electricalhog/PD_Charger/KiCad/EPC-KiCad-Library/Ki3DModels/D0375.step

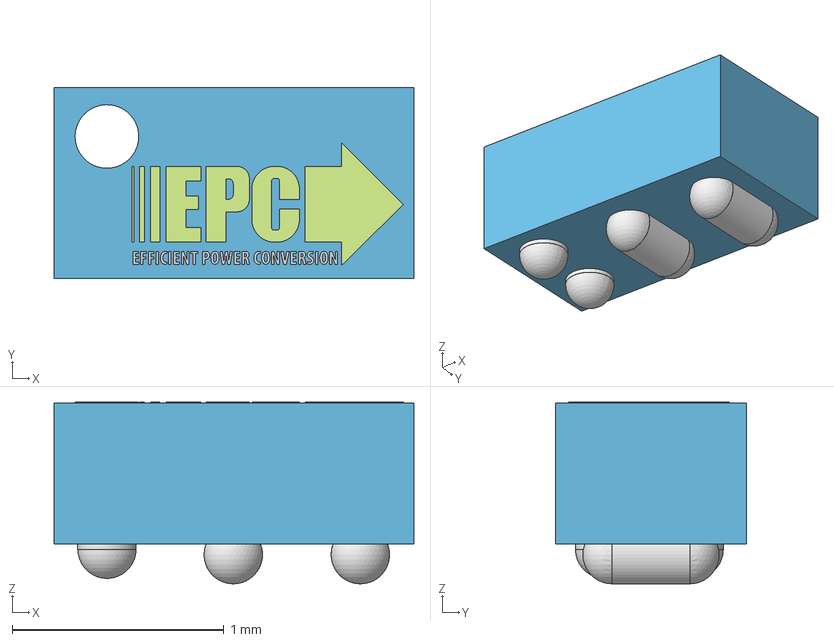
[picture p19: CAD file, 2024-12-06]
KiCad/EPC-KiCad-Library/Ki3DModels/D0375.step
1.70 x 0.9 x 0.858 mm
1.25mm
1.25mm001
1.25mm002
1.25mm003
1.25mm004
1.25mm005
1.25mm006
Extruded
