electricalhog/PD_Charger/KiCad/EPC-KiCad-Library/Ki3DModels/D0551.step

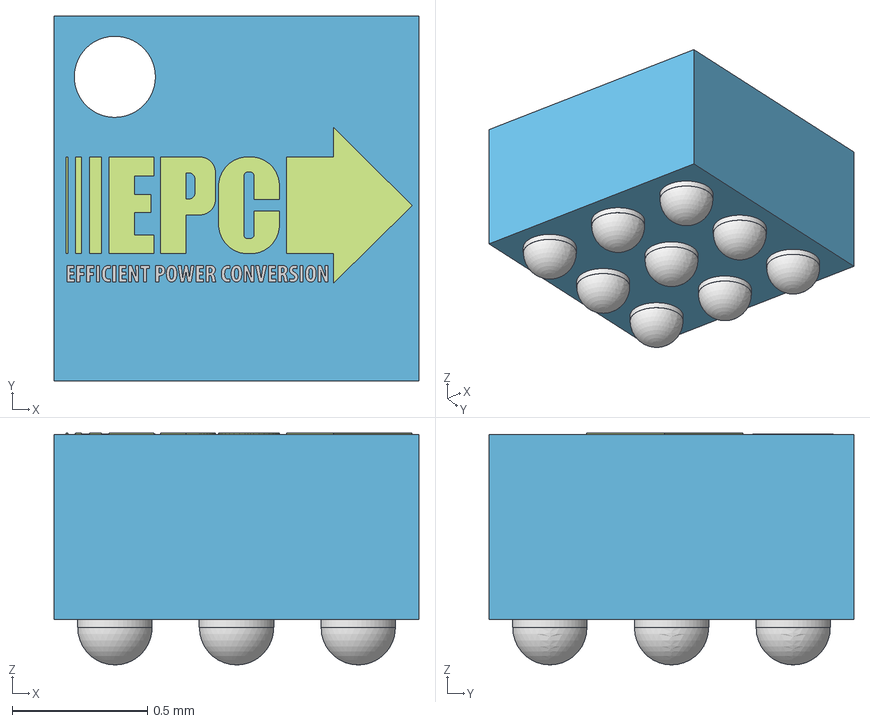
[picture p20: CAD file, 2024-12-06]
KiCad/EPC-KiCad-Library/Ki3DModels/D0551.step
1.35 x 1.35 x 0.857 mm
1.25mm
1.25mm001
1.25mm002
1.25mm003
1.25mm004
1.25mm005
1.25mm006
Extruded
