electricalhog/PD_Charger/KiCad/EPC-KiCad-Library/Ki3DModels/D0683.step

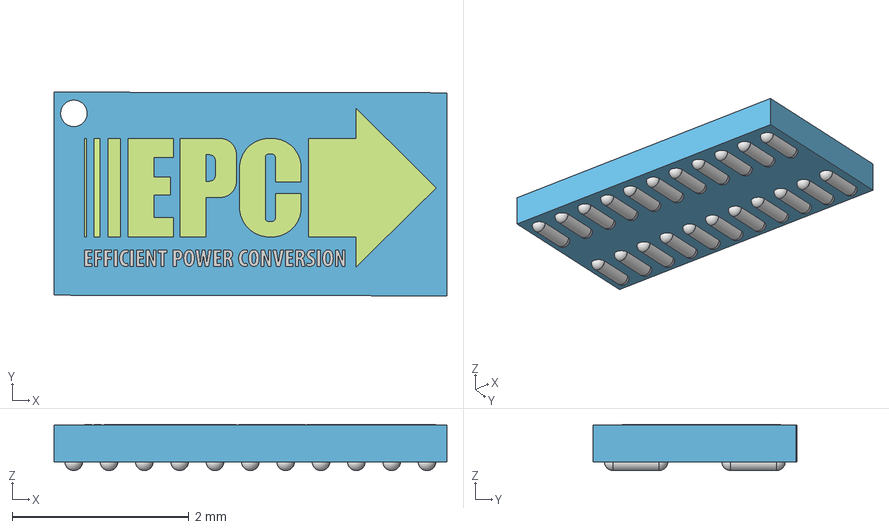
[picture p21: CAD file, 2024-12-06]
KiCad/EPC-KiCad-Library/Ki3DModels/D0683.step
4.45 x 2.31 x 0.523 mm
Green001
Green002
Green003
Green004
Green005
Green006
Green007
Extruded
