electricalhog/PD_Charger/KiCad/EPC-KiCad-Library/Ki3DModels/D0034.step

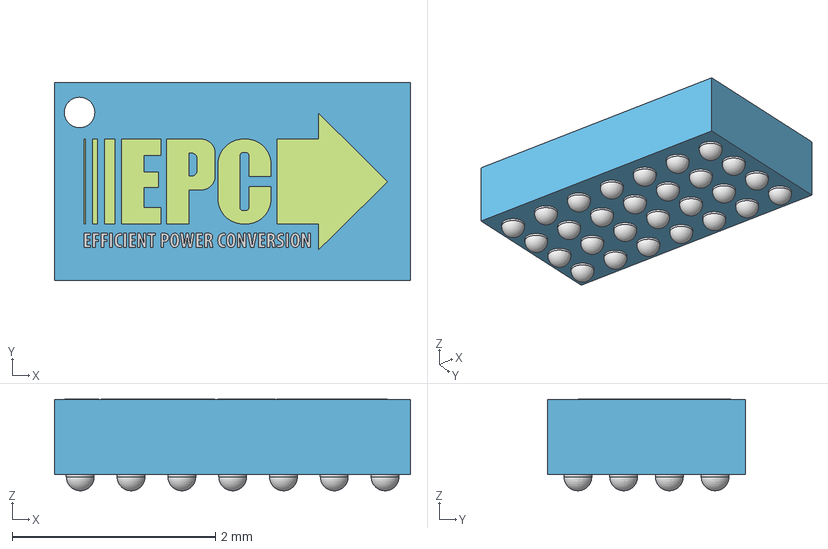
[picture p22: CAD file, 2024-12-06]
KiCad/EPC-KiCad-Library/Ki3DModels/D0034.step
3.50 x 1.95 x 0.902 mm
Green001
Green002
Green003
Green004
Green005
Green006
Green007
Extruded
