electricalhog/PD_Charger/KiCad/EPC-KiCad-Library/Ki3DModels/D0265.step

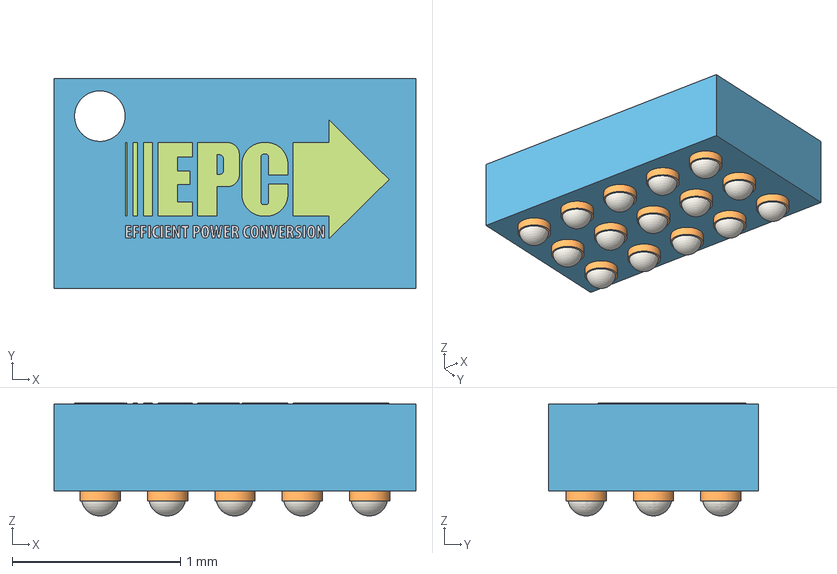
[picture p23: CAD file, 2024-12-06]
KiCad/EPC-KiCad-Library/Ki3DModels/D0265.step
2.15 x 1.25 x 0.671 mm
1.5mm
1.5mm001
1.5mm002
1.5mm003
1.5mm004
1.5mm005
1.5mm006
Extruded
