electricalhog/PD_Charger/KiCad/EPC-KiCad-Library/Ki3DModels/D0122.step

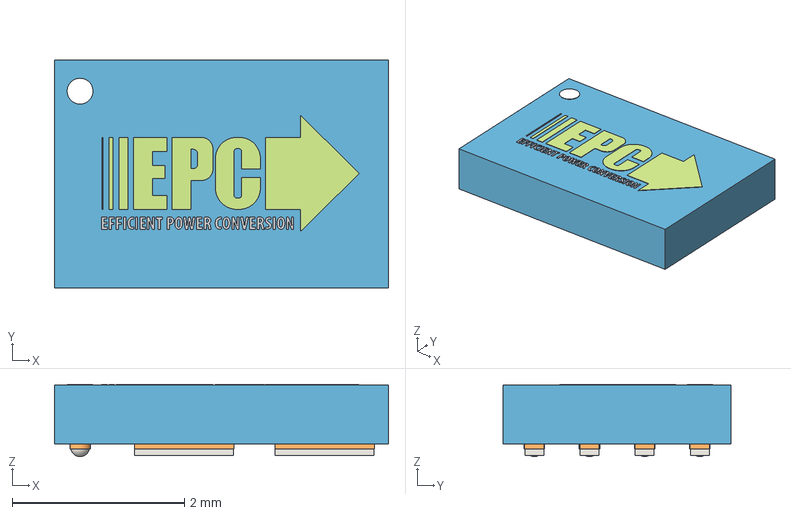
[picture p24: CAD file, 2024-12-06]
KiCad/EPC-KiCad-Library/Ki3DModels/D0122.step
3.88 x 2.64 x 0.838 mm
Green001
Green002
Green003
Green004
Green005
Green006
Green007
Extruded
Extruded001 x 8
Extruded002 x 8
