electricalhog/PD_Charger/KiCad/EPC-KiCad-Library/Ki3DModels/D0298.step

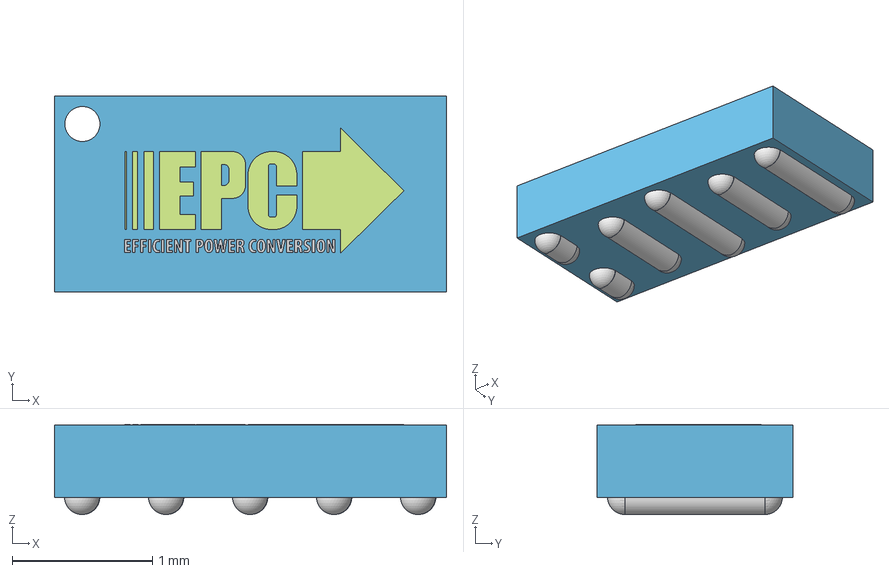
[picture p25: CAD file, 2024-12-06]
KiCad/EPC-KiCad-Library/Ki3DModels/D0298.step
2.80 x 1.40 x 0.643 mm
2mm
2mm001
2mm002
2mm003
2mm004
2mm005
2mm006
Extruded
