electricalhog/PD_Charger/KiCad/EPC-KiCad-Library/Ki3DModels/D0606F.step

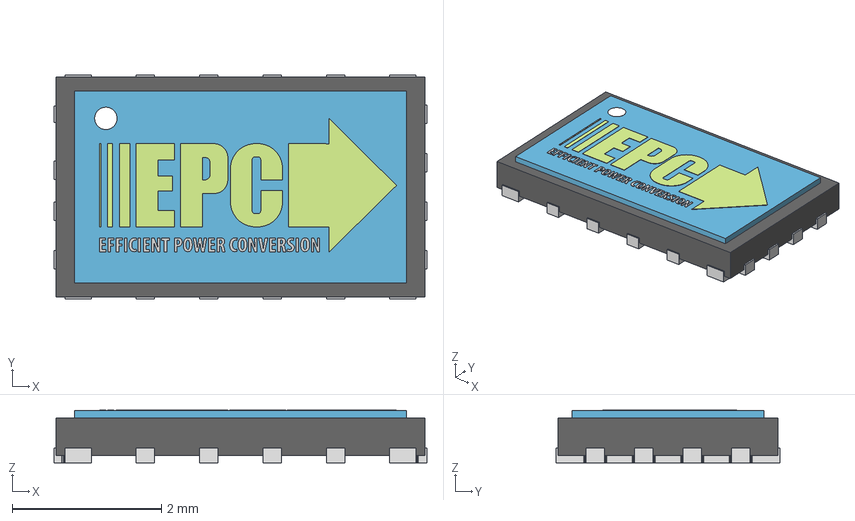
[picture p27: CAD file, 2024-12-06]
KiCad/EPC-KiCad-Library/Ki3DModels/D0606F.step
5.00 x 3.00 x 0.705 mm
Green001
Green002
Green003
Green004
Green005
Green006
Green007
Extruded
Extruded001
Extruded002
Extruded003
Extruded004 x 4
Extruded008
