electricalhog/PD_Charger/KiCad/EPC-KiCad-Library/Ki3DModels/D0617.step

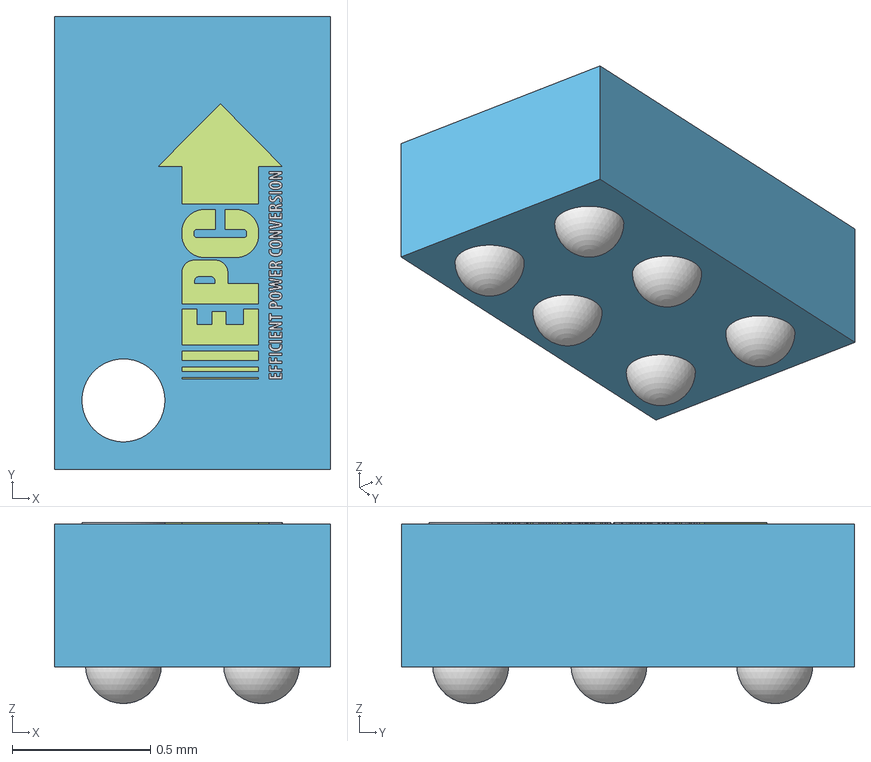
[picture p28: CAD file, 2024-12-06]
KiCad/EPC-KiCad-Library/Ki3DModels/D0617.step
1 x 1.64 x 0.656 mm
1mm
1mm001
1mm002
1mm003
1mm004
1mm005
1mm006
Extruded
