electricalhog/PD_Charger/KiCad/EPC-KiCad-Library/Ki3DModels/D0540.step

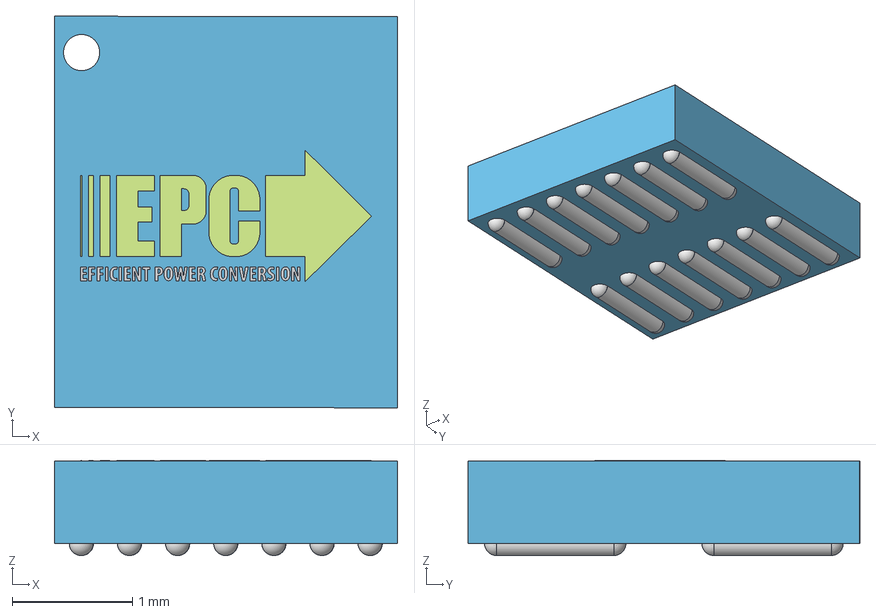
[picture p29: CAD file, 2024-12-06]
KiCad/EPC-KiCad-Library/Ki3DModels/D0540.step
2.85 x 3.25 x 0.79 mm
2.5mm
2.5mm001
2.5mm002
2.5mm003
2.5mm004
2.5mm005
2.5mm006
Extruded
