electricalhog/PD_Charger/KiCad/EPC-KiCad-Library/Ki3DModels/D0826T44M.step

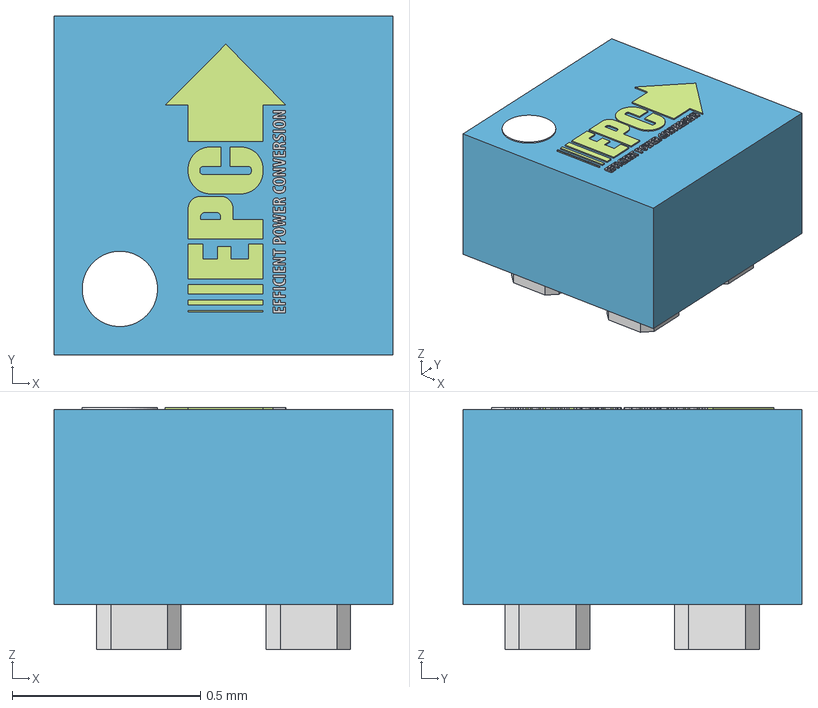
[picture p30: CAD file, 2024-12-06]
KiCad/EPC-KiCad-Library/Ki3DModels/D0826T44M.step
0.9 x 0.9 x 0.643 mm
.75mm
.75mm001
.75mm002
.75mm003
.75mm004
.75mm005
.75mm006
Extruded
Extruded001 x 4
