electricalhog/PD_Charger/KiCad/EPC-KiCad-Library/Ki3DModels/D0870.step

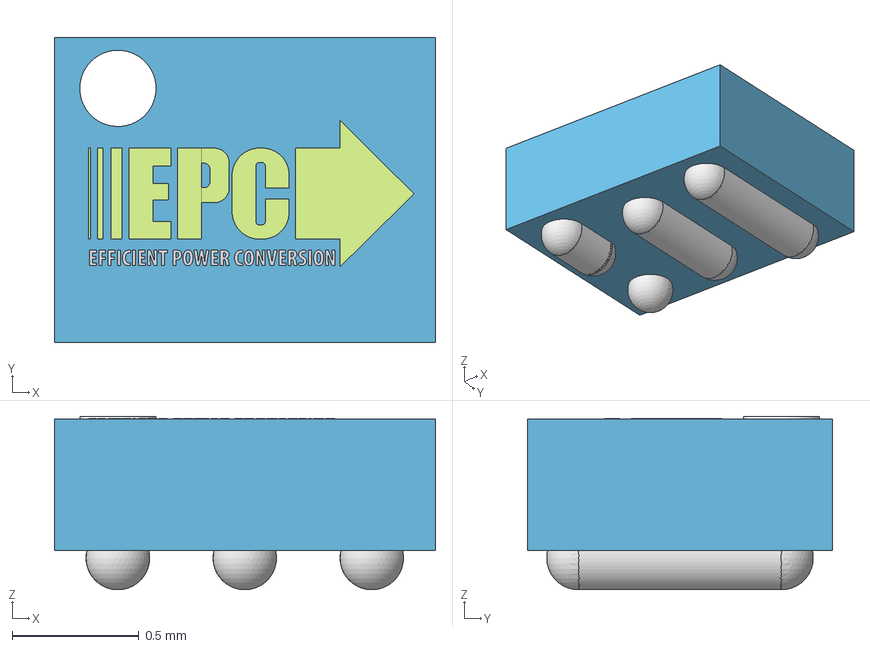
[picture p31: CAD file, 2024-12-06]
KiCad/EPC-KiCad-Library/Ki3DModels/D0870.step
1.50 x 1.20 x 0.683 mm
3D_EPClogo1_25mm
3D_EPClogo1_25mm001
3D_EPClogo1_25mm002
3D_EPClogo1_25mm003
3D_EPClogo1_25mm004
3D_EPClogo1_25mm005
3D_EPClogo1_25mm006
3D_EPClogo1_25mm007
3D_EPClogo1_25mm009
3D_EPClogo1_25mm010
3D_EPClogo1_25mm011
3D_EPClogo1_25mm012
3D_EPClogo1_25mm013
3D_EPClogo1_25mm014
3D_EPClogo1_25mm015
3D_EPClogo1_25mm016
3D_EPClogo1_25mm017
3D_EPClogo1_25mm018
3D_EPClogo1_25mm019
3D_EPClogo1_25mm020
3D_EPClogo1_25mm021
3D_EPClogo1_25mm022
3D_EPClogo1_25mm023
3D_EPClogo1_25mm024
3D_EPClogo1_25mm025
3D_EPClogo1_25mm026
3D_EPClogo1_25mm027
3D_EPClogo1_25mm028
3D_EPClogo1_25mm029
3D_EPClogo1_25mm030
3D_EPClogo1_25mm031
3D_EPClogo1_25mm032
Extruded
