electricalhog/PD_Charger/KiCad/EPC-KiCad-Library/Ki3DModels/D0727.step

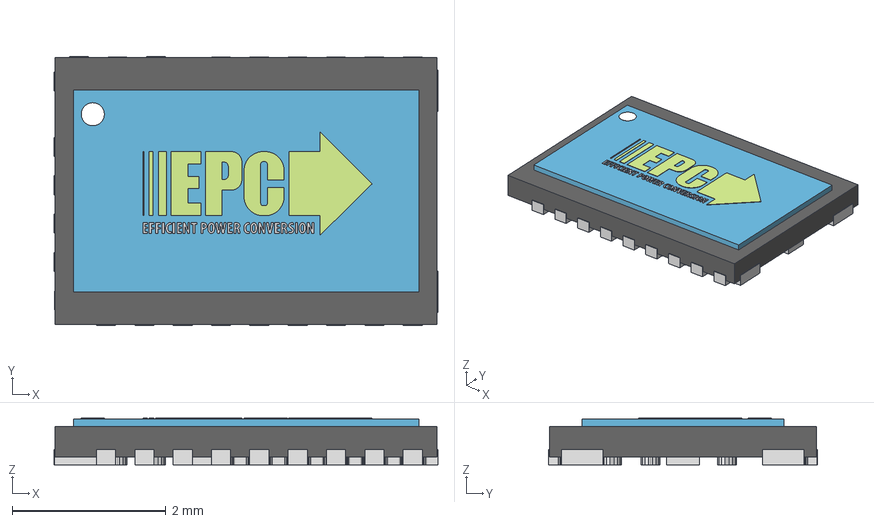
[picture p32: CAD file, 2024-12-06]
KiCad/EPC-KiCad-Library/Ki3DModels/D0727.step
5.00 x 3.50 x 0.61 mm
Green001
Green002
Green003
Green004
Green005
Green006
Green007
Extruded
Extruded001
Extruded002
Extruded003
Extruded004 x 2
Extruded006
Extruded007 x 3
Extruded010
Extruded011
Extruded012
Extruded013 x 2
