electricalhog/PD_Charger/KiCad/EPC-KiCad-Library/Ki3DModels/D0331.step

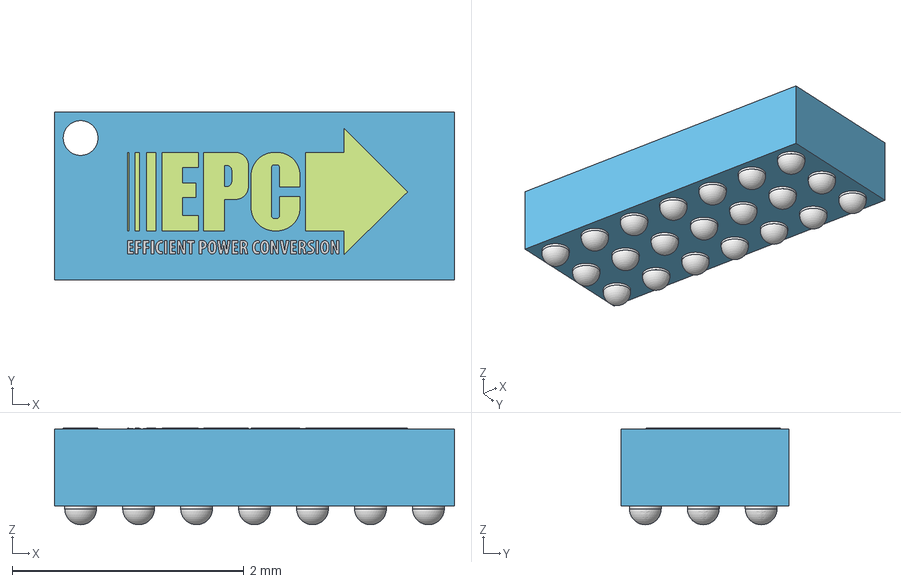
[picture p33: CAD file, 2024-12-06]
KiCad/EPC-KiCad-Library/Ki3DModels/D0331.step
3.45 x 1.45 x 0.832 mm
2.5mm
2.5mm001
2.5mm002
2.5mm003
2.5mm004
2.5mm005
2.5mm006
Extruded
