electricalhog/PD_Charger/KiCad/EPC-KiCad-Library/Ki3DModels/D0727u.step

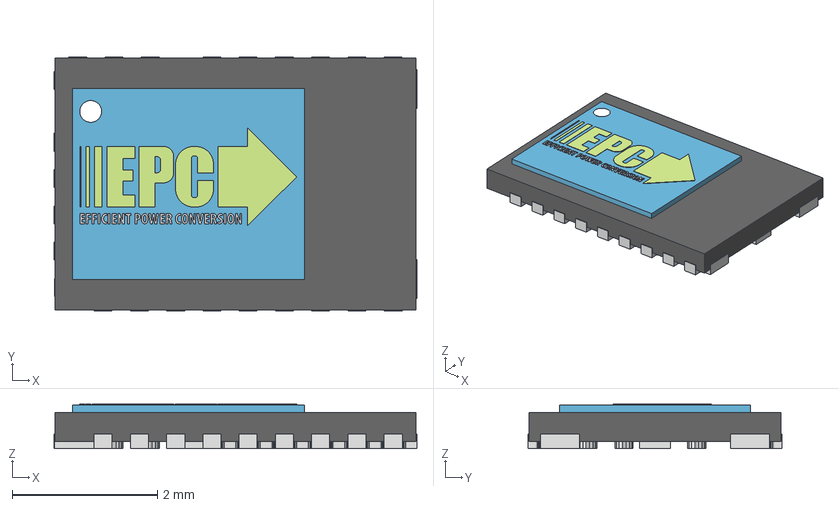
[picture p36: CAD file, 2024-12-06]
KiCad/EPC-KiCad-Library/Ki3DModels/D0727u.step
5.00 x 3.50 x 0.61 mm
Green001
Green002
Green003
Green004
Green005
Green006
Green007
Extruded x 2
Extruded002
Extruded003
Extruded004
Extruded005 x 3
Extruded008
Extruded009 x 2
Extruded011
Extruded012
Extruded013
Extruded014
