electricalhog/PD_Charger/KiCad/EPC-KiCad-Library/Ki3DModels/D0133.step

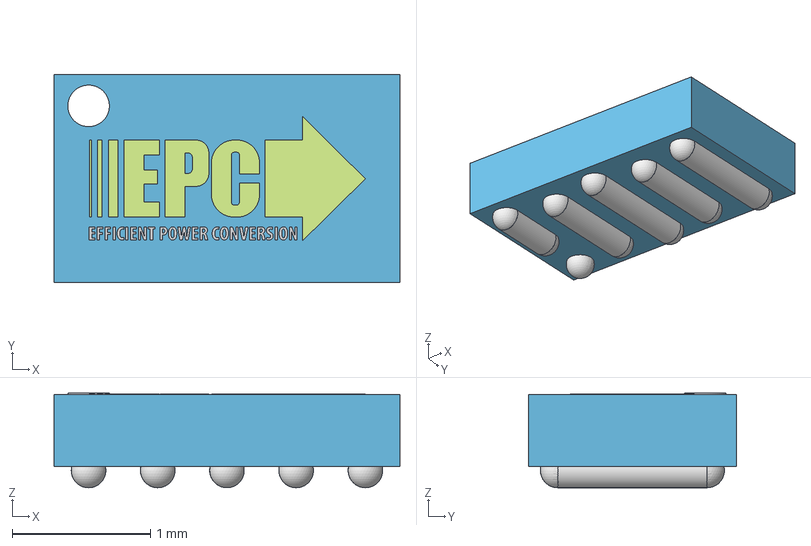
[picture p37: CAD file, 2024-12-06]
KiCad/EPC-KiCad-Library/Ki3DModels/D0133.step
2.50 x 1.50 x 0.683 mm
2mm
2mm001
2mm002
2mm003
2mm004
2mm005
2mm006
Extruded
