electricalhog/PD_Charger/KiCad/EPC-KiCad-Library/Ki3DModels/D0629.step

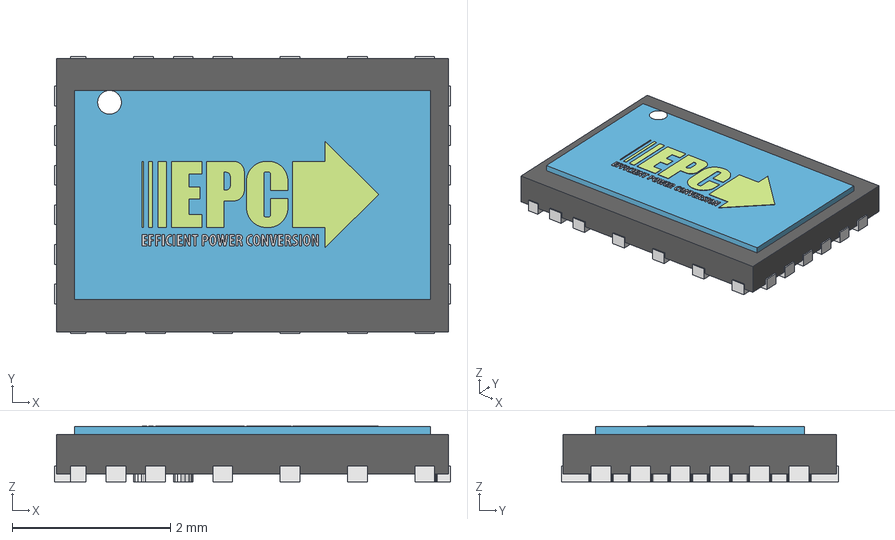
[picture p38: CAD file, 2024-12-06]
KiCad/EPC-KiCad-Library/Ki3DModels/D0629.step
5.00 x 3.50 x 0.705 mm
Green001
Green002
Green003
Green004
Green005
Green006
Green007
Extruded
Extruded001 x 3
Extruded004
Extruded005 x 2
Extruded007 x 4
Extruded011 x 2
Extruded013
Extruded014
Extruded015
