electricalhog/PD_Charger/KiCad/EPC-KiCad-Library/Ki3DModels/D0177.step

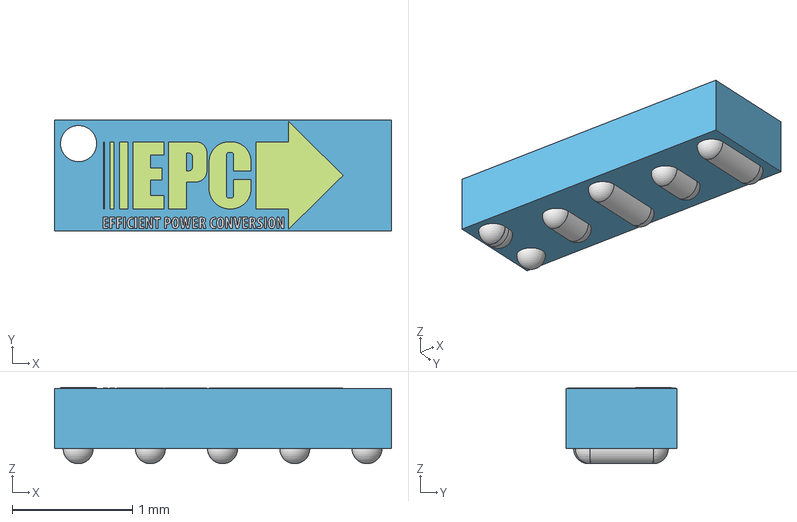
[picture p39: CAD file, 2024-12-06]
KiCad/EPC-KiCad-Library/Ki3DModels/D0177.step
2.80 x 0.92 x 0.635 mm
2mm
2mm001
2mm002
2mm003
2mm004
2mm005
2mm006
Extruded
