electricalhog/PD_Charger/KiCad/EPC-KiCad-Library/Ki3DModels/D0364.step

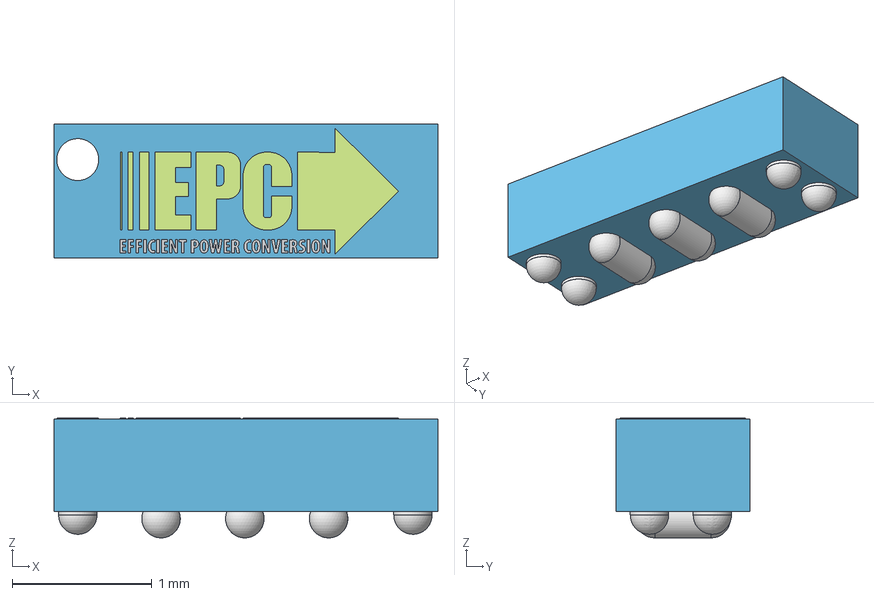
[picture p40: CAD file, 2024-12-06]
KiCad/EPC-KiCad-Library/Ki3DModels/D0364.step
2.75 x 0.96 x 0.858 mm
2mm
2mm001
2mm002
2mm003
2mm004
2mm005
2mm006
Extruded
