electricalhog/PD_Charger/KiCad/EPC-KiCad-Library/Ki3DModels/D0496.step

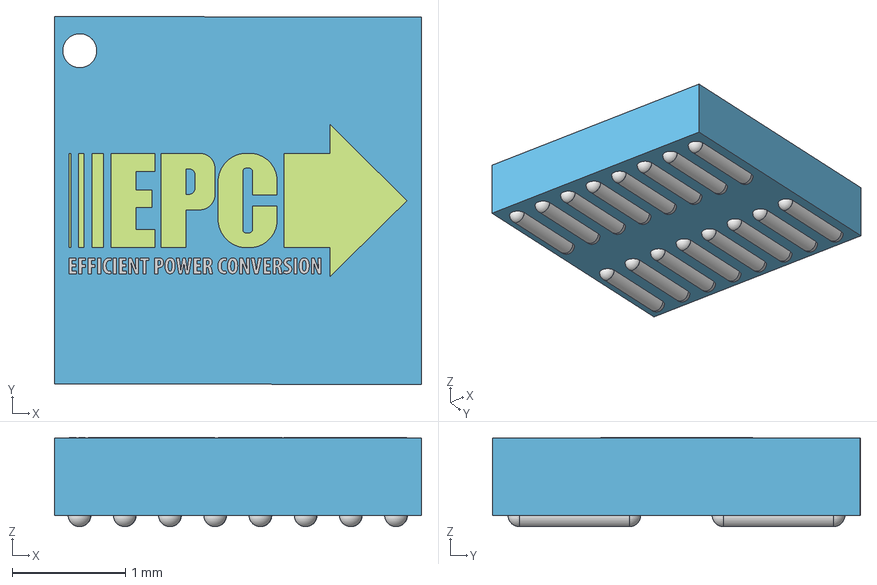
[picture p43: CAD file, 2024-12-06]
KiCad/EPC-KiCad-Library/Ki3DModels/D0496.step
3.25 x 3.26 x 0.79 mm
Green001
Green002
Green003
Green004
Green005
Green006
Green007
Extruded
