electricalhog/PD_Charger/KiCad/EPC-KiCad-Library/Ki3DModels/D0210.step

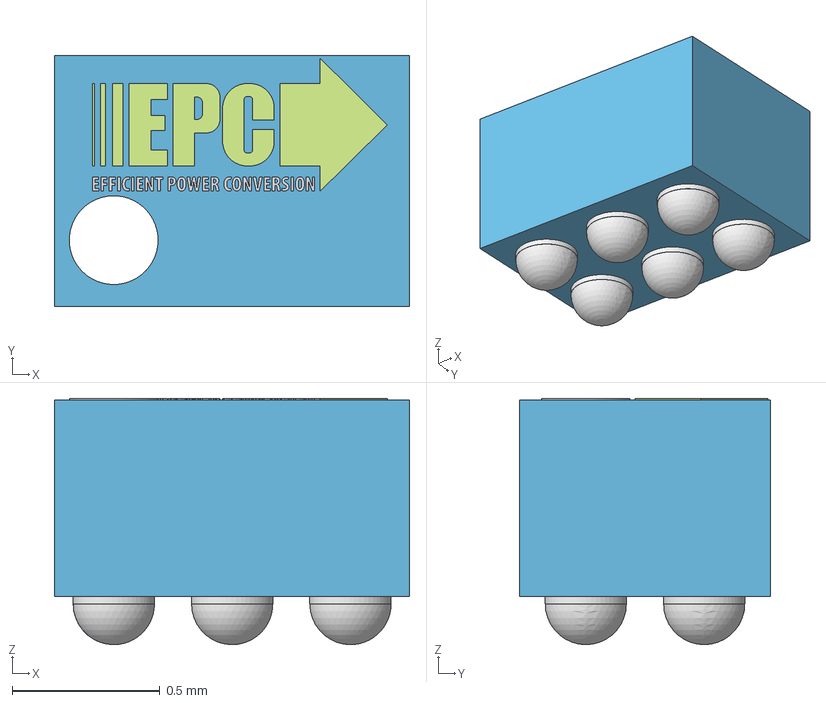
[picture p45: CAD file, 2024-12-06]
KiCad/EPC-KiCad-Library/Ki3DModels/D0210.step
1.20 x 0.85 x 0.833 mm
1mm
1mm001
1mm002
1mm003
1mm004
1mm005
1mm006
Extruded
