electricalhog/PD_Charger/KiCad/EPC-KiCad-Library/Ki3DModels/D0353.step

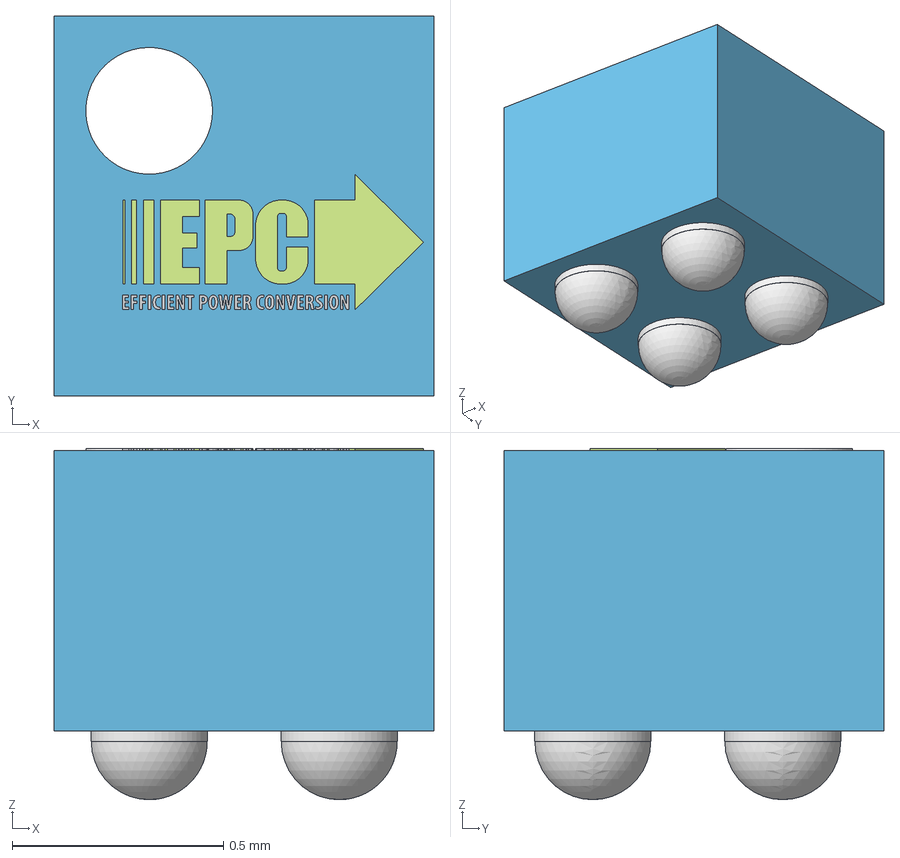
[picture p46: CAD file, 2024-12-06]
KiCad/EPC-KiCad-Library/Ki3DModels/D0353.step
0.9 x 0.9 x 0.832 mm
.75mm
.75mm001
.75mm002
.75mm003
.75mm004
.75mm005
.75mm006
Extruded
